stojnev/dwr-gwyfyn/Counterweight/STL/Counterweight - Counterweight Slider.stl

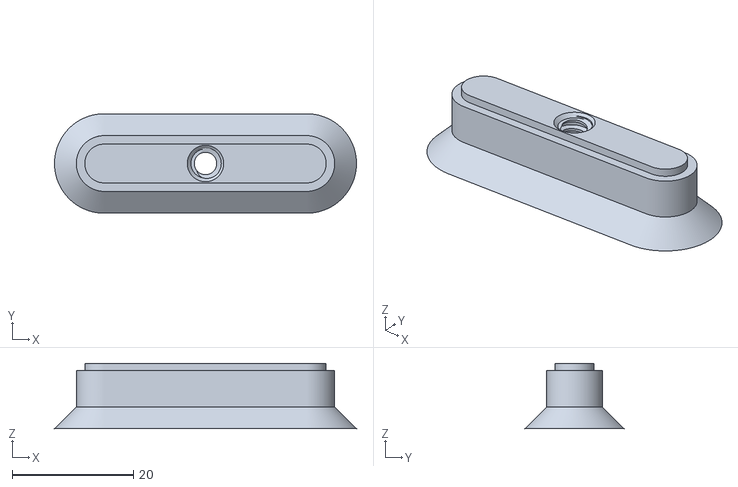
[picture p16: CAD file, 2026-01-21]
Counterweight/STL/Counterweight - Counterweight Slider.stl
49.8 x 16.4 x 10.8
