stojnev/dwr-gwyfyn/Pillar/STL/Tonearm Pillar - Pillar Body.stl

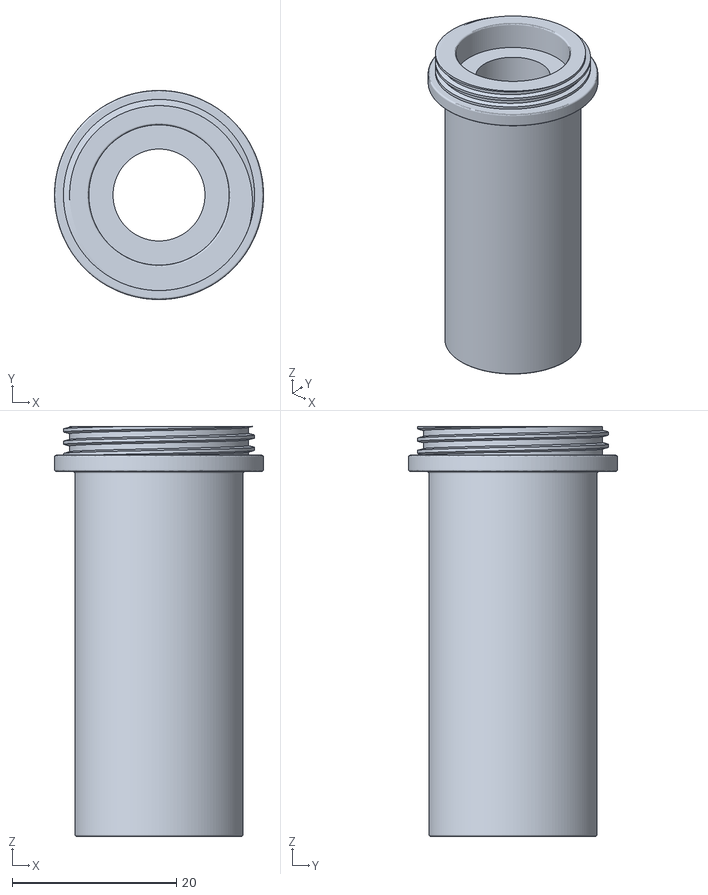
[picture p17: CAD file, 2026-01-14]
Pillar/STL/Tonearm Pillar - Pillar Body.stl
25.5 x 25.5 x 50.0
