stojnev/dwr-gwyfyn/Rest/STL/Tonearm Rest Modular - Tonearm Rest.stl

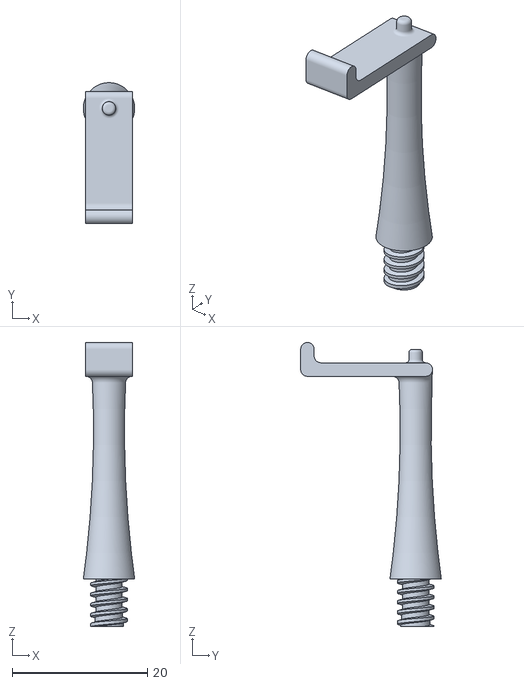
[picture p18: CAD file, 2026-01-17]
Rest/STL/Tonearm Rest Modular - Tonearm Rest.stl
7.60 x 20.8 x 42.0
