stojnev/dwr-gwyfyn/Tube/STL/Peripherals/Bearing Mount - Flexure Mount Cap.stl

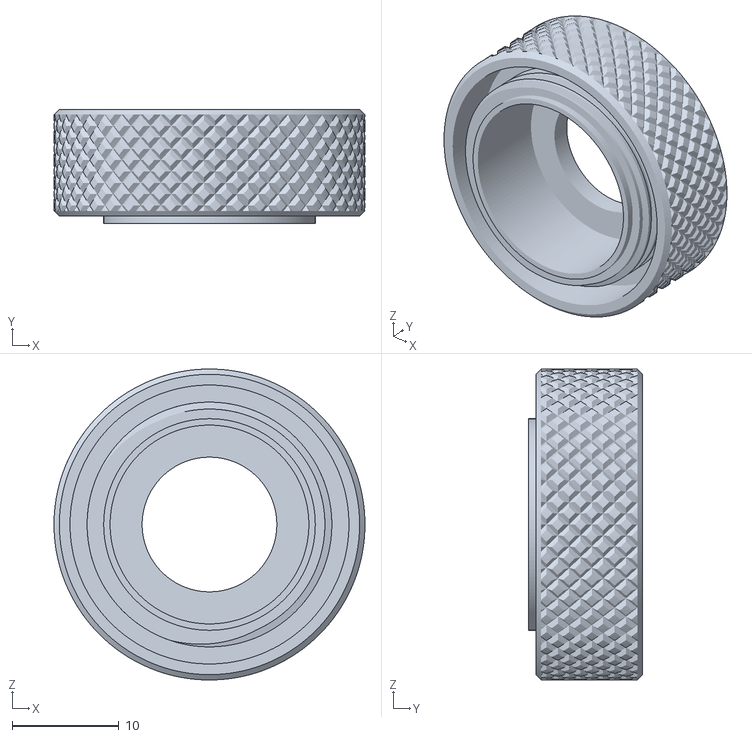
[picture p19: CAD file, 2026-02-07]
Tube/STL/Peripherals/Bearing Mount - Flexure Mount Cap.stl
29.1 x 10.7 x 29.1
