stojnev/dwr-gwyfyn/Base/STL/SME Mount - SME Clamp Collar.stl

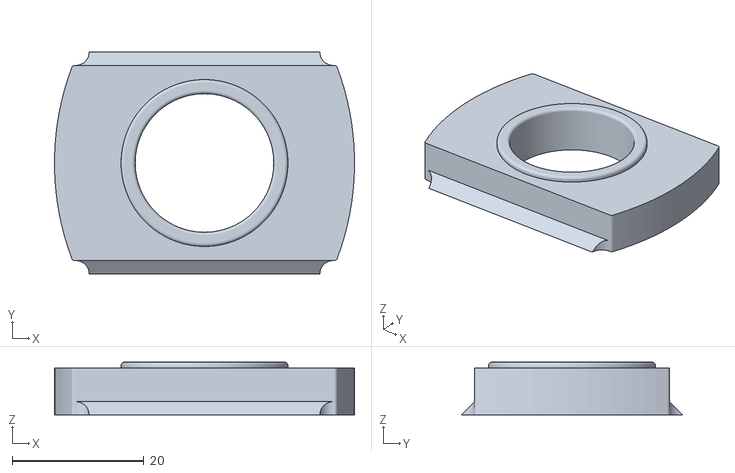
[picture p20: CAD file, 2026-01-13]
Base/STL/SME Mount - SME Clamp Collar.stl
45.5 x 33.6 x 8.00
