stojnev/dwr-gwyfyn/Counterweight/STL/Counterweight - Counterweight Base.stl

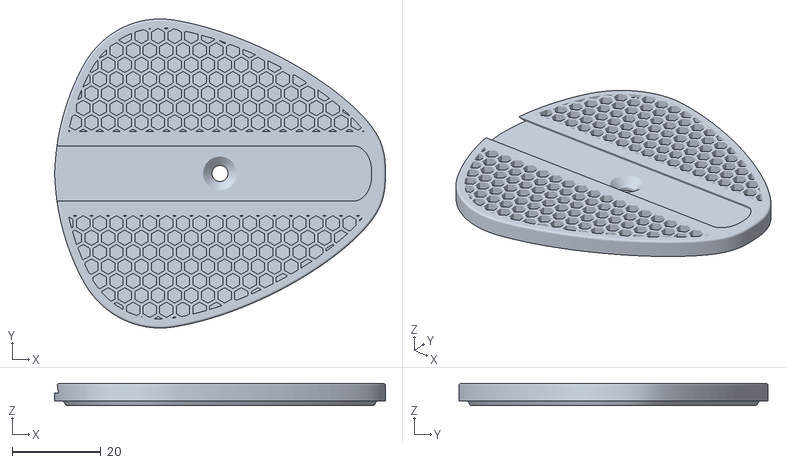
[picture p21: CAD file, 2026-01-21]
Counterweight/STL/Counterweight - Counterweight Base.stl
74.6 x 69.6 x 5.00
