stojnev/dwr-gwyfyn/Rest/STL/Tonearm Rest Modular - Connector Support.stl

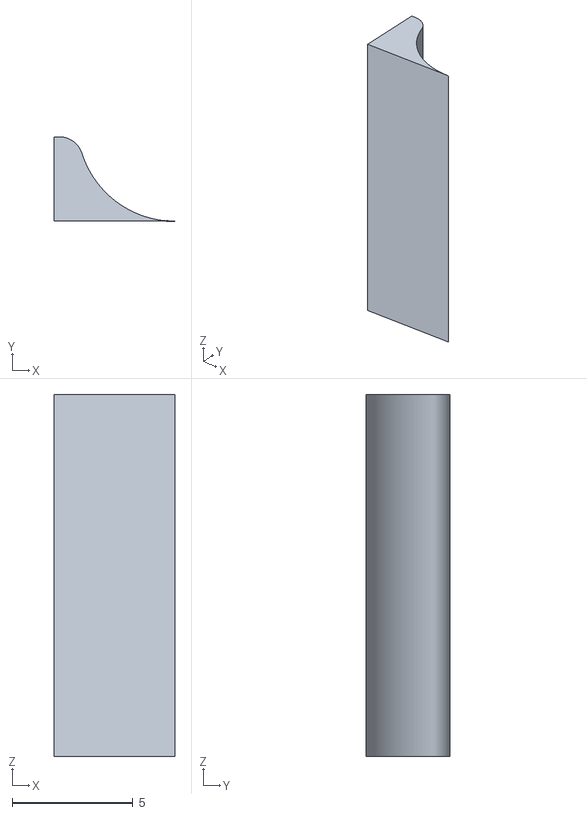
[picture p22: CAD file, 2026-01-17]
Rest/STL/Tonearm Rest Modular - Connector Support.stl
5.00 x 3.50 x 15.0
