stojnev/dwr-gwyfyn/Base/STL/SME Fixed Mount - SME Fixed Mount.stl

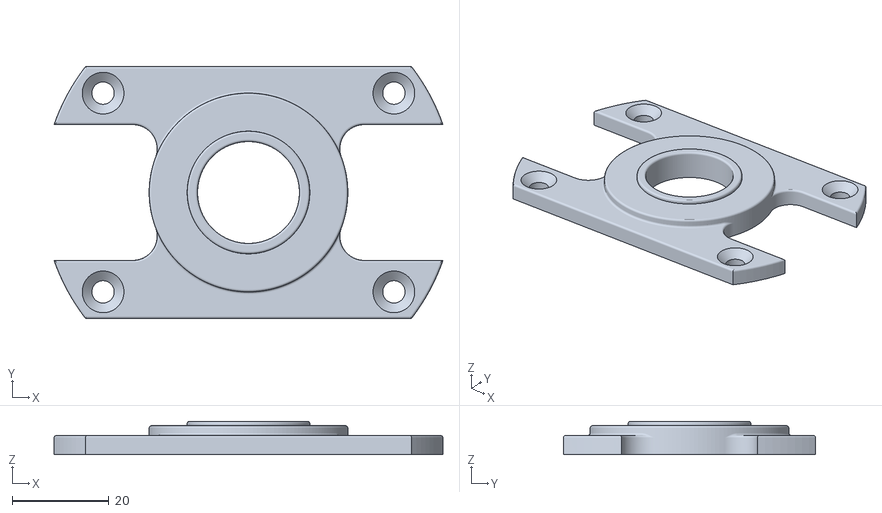
[picture p23: CAD file, 2026-01-13]
Base/STL/SME Fixed Mount - SME Fixed Mount.stl
80.3 x 52.0 x 6.90
