stojnev/dwr-gwyfyn/Rest/STL/Tonearm Rest Modular - Tonearm Plate.stl

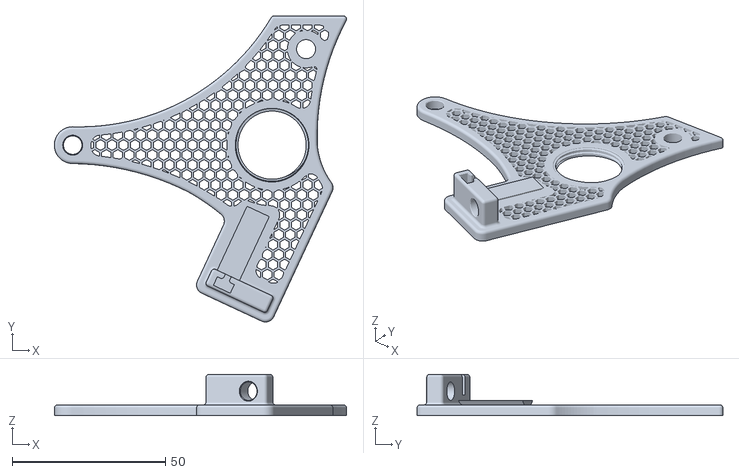
[picture p24: CAD file, 2026-01-17]
Rest/STL/Tonearm Rest Modular - Tonearm Plate.stl
95.3 x 99.7 x 13.5
