stojnev/dwr-gwyfyn/Base/STL/Helicoidal VTA - Adjustment Ring.stl

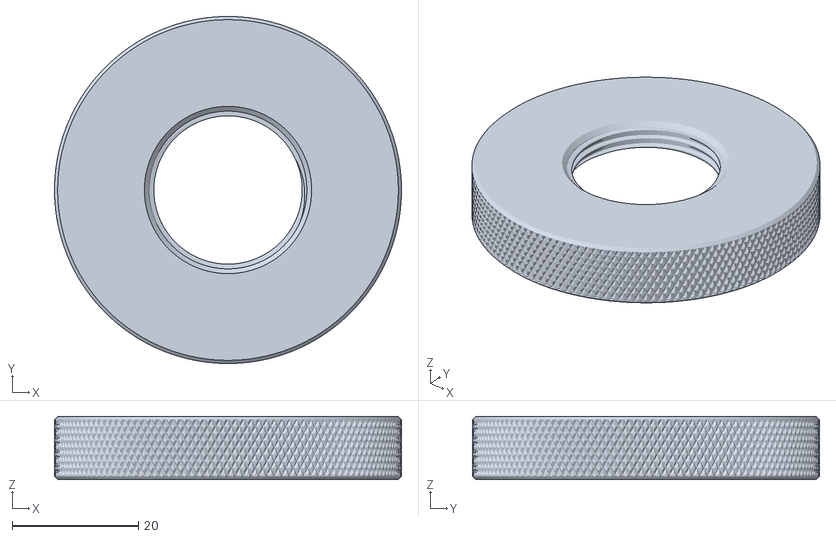
[picture p25: CAD file, 2026-01-13]
Base/STL/Helicoidal VTA - Adjustment Ring.stl
55.0 x 55.0 x 10.0
