stojnev/dwr-gwyfyn/Base/STL/Helicoidal VTA - VTA Base.stl

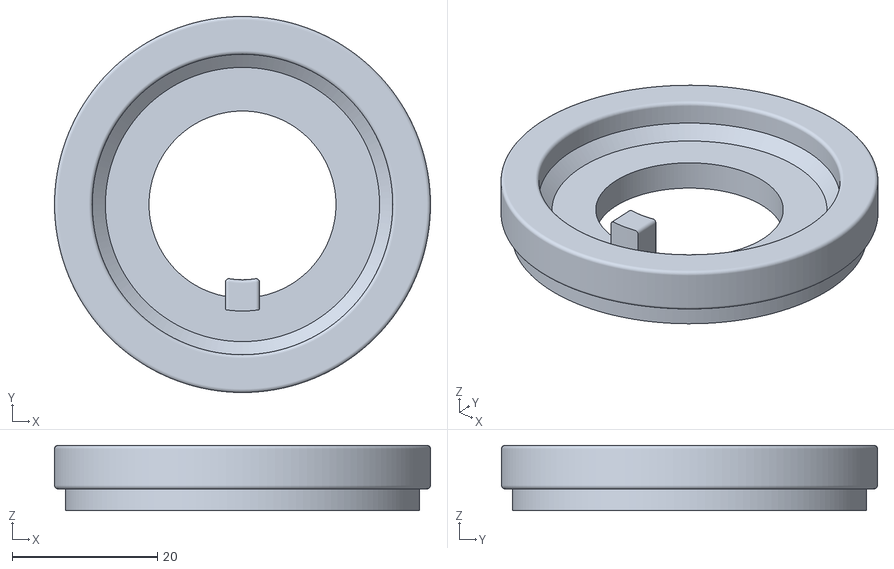
[picture p26: CAD file, 2026-01-13]
Base/STL/Helicoidal VTA - VTA Base.stl
51.7 x 51.7 x 9.00
