stojnev/dwr-gwyfyn/Rest/STL/Tonearm Rest Modular - Wiring Cover RCA.stl

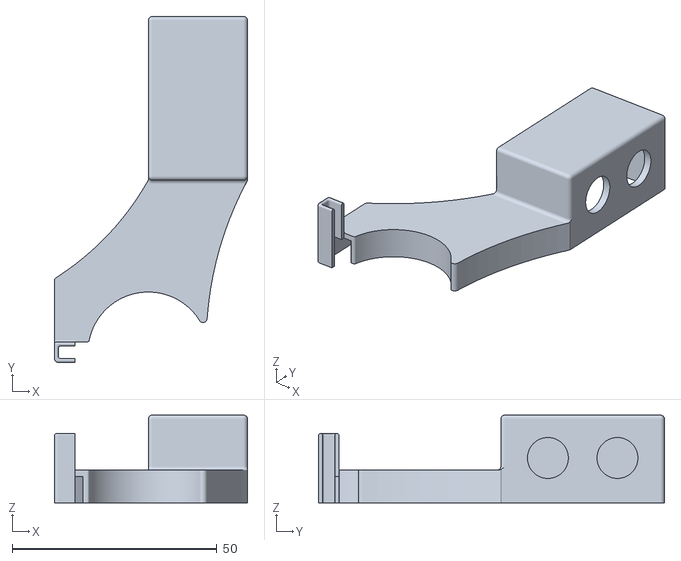
[picture p27: CAD file, 2026-01-17]
Rest/STL/Tonearm Rest Modular - Wiring Cover RCA.stl
47.3 x 84.6 x 21.5
