stojnev/dwr-gwyfyn/Base/STL/SME Mount - SME Base.stl

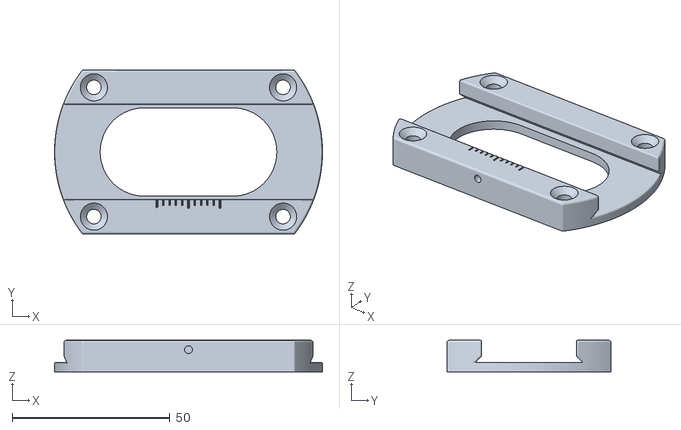
[picture p28: CAD file, 2026-01-13]
Base/STL/SME Mount - SME Base.stl
85.0 x 52.0 x 10.0
