stojnev/dwr-gwyfyn/Rest/STL/Tonearm Rest Modular - Wiring Cover DIN.stl

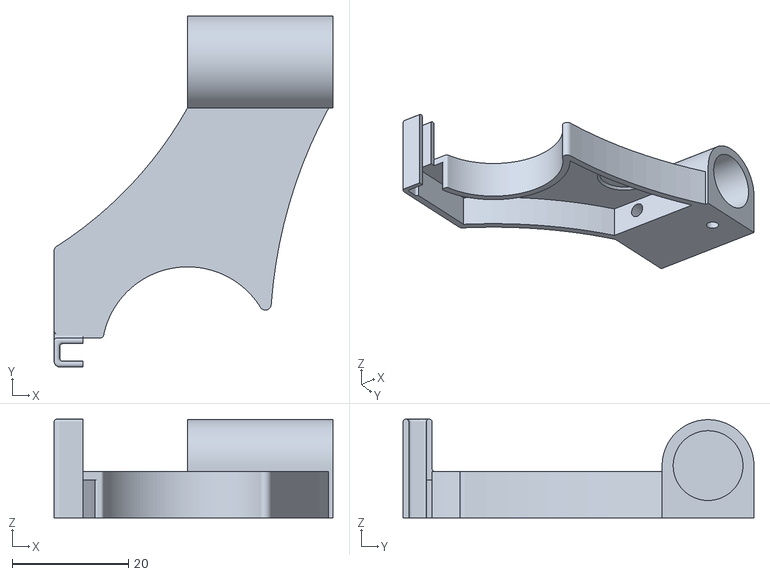
[picture p29: CAD file, 2026-01-17]
Rest/STL/Tonearm Rest Modular - Wiring Cover DIN.stl
48.0 x 60.4 x 17.0
