stojnev/dwr-gwyfyn/Base/STL/Helicoidal VTA - Tonearm Collar.stl

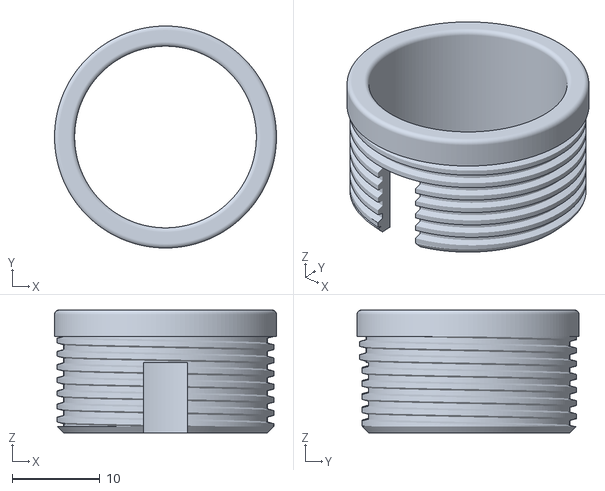
[picture p30: CAD file, 2026-01-13]
Base/STL/Helicoidal VTA - Tonearm Collar.stl
25.3 x 25.3 x 14.0
