stojnev/dwr-gwyfyn/Alignment/Spindle Distance Jig/Assemblies/Spindle Distance Jig Universal.png

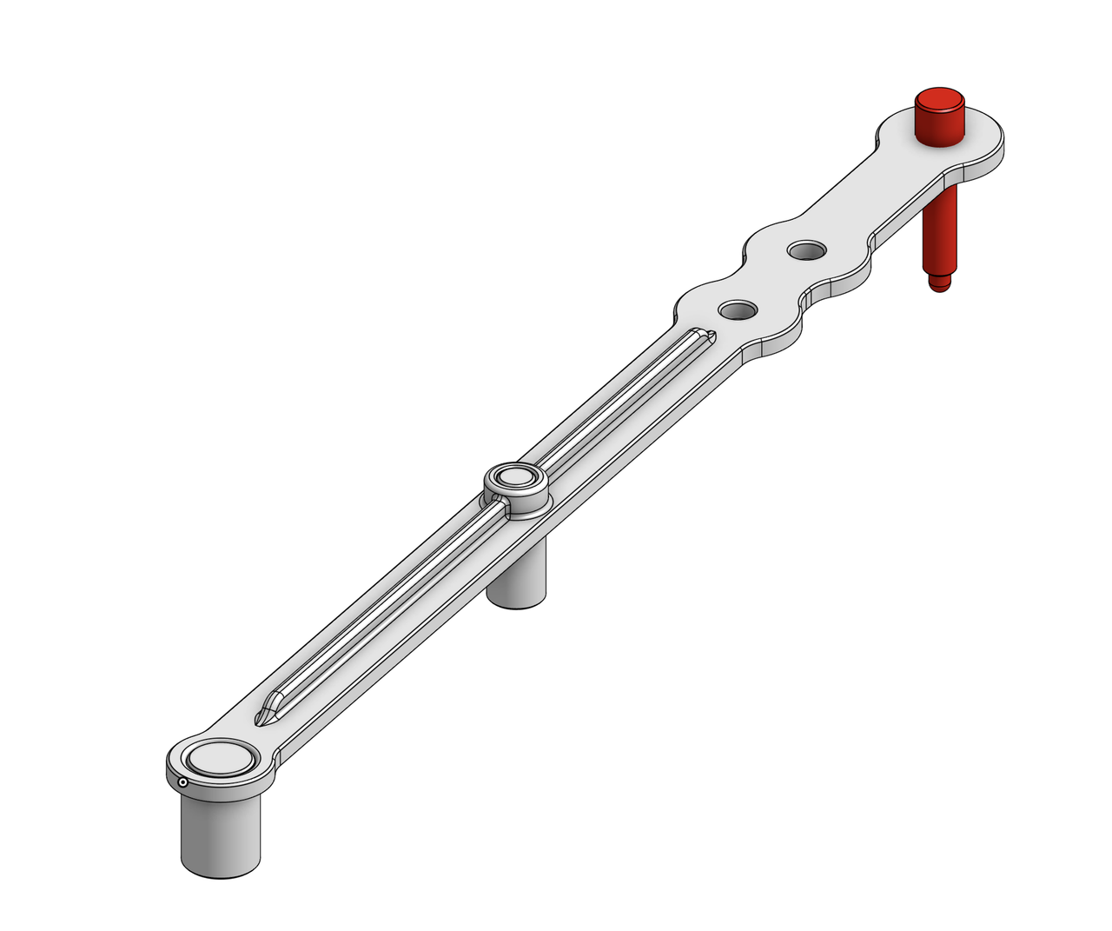
Alignment/Spindle Distance Jig/Assemblies/Spindle Distance Jig Universal.png
