stojnev/dwr-gwyfyn/Alignment/Spindle Distance Jig/Assemblies/Spindle Distance Jig.png

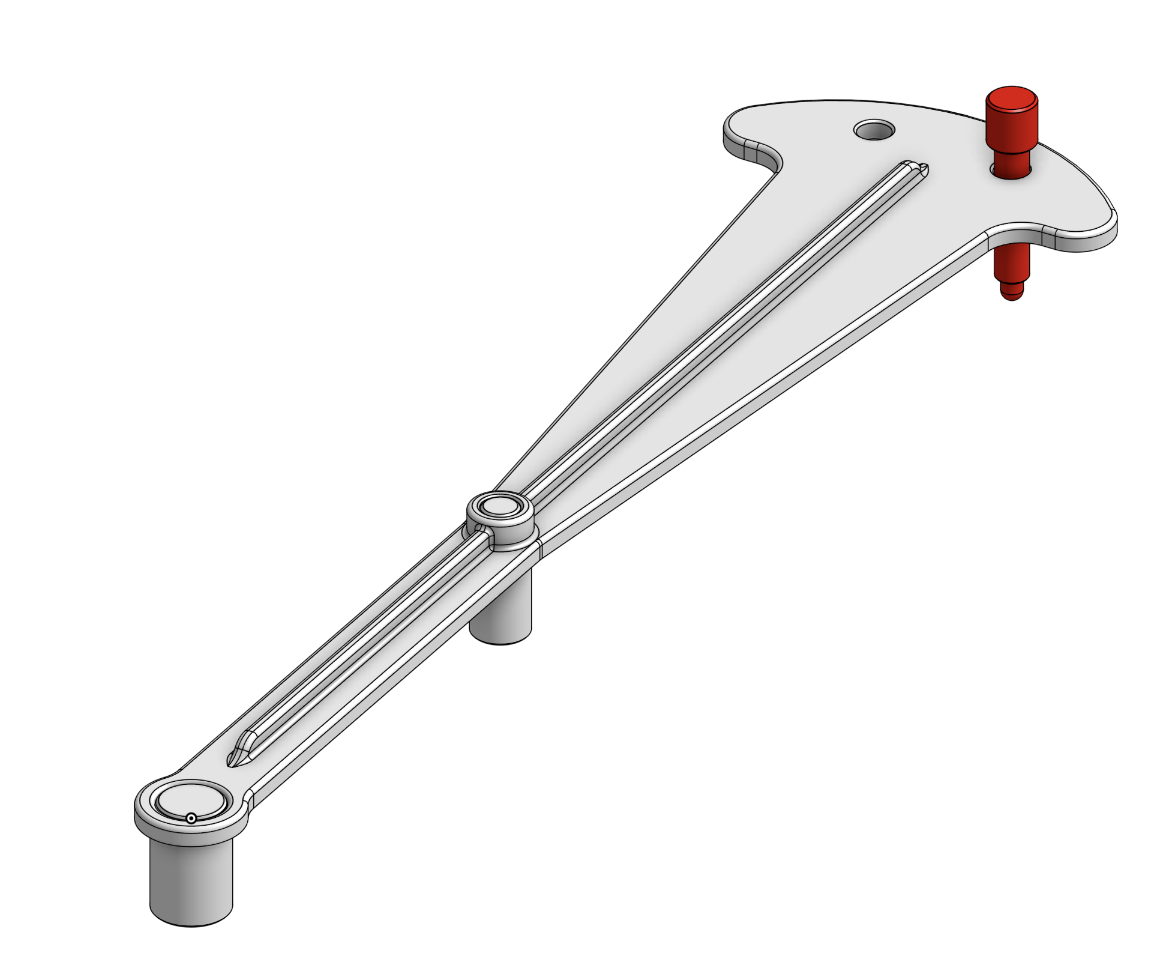
Alignment/Spindle Distance Jig/Assemblies/Spindle Distance Jig.png
