stojnev/dwr-gwyfyn/Base/Assemblies/SME Fixed VTA Clamp Mount [FULL].png

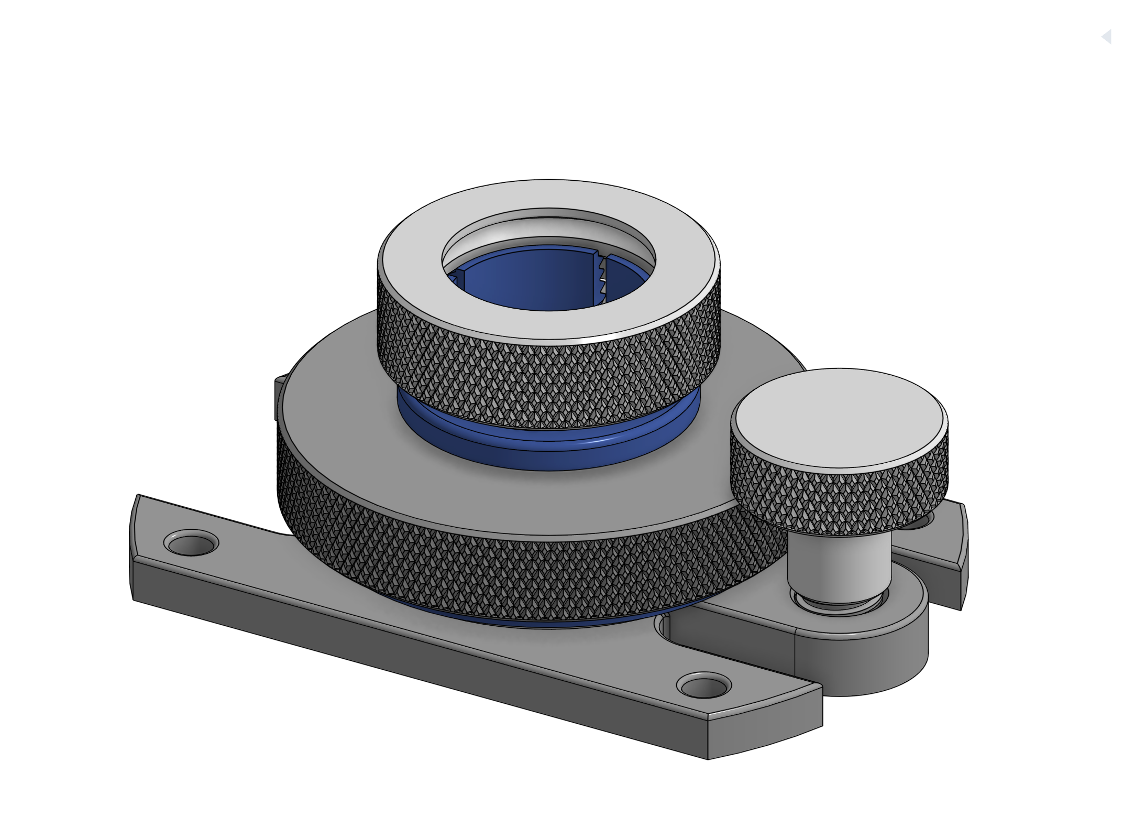
Base/Assemblies/SME Fixed VTA Clamp Mount [FULL].png
