stojnev/dwr-gwyfyn/Base/Assemblies/SME Sliding Clamp Mount [FULL].png

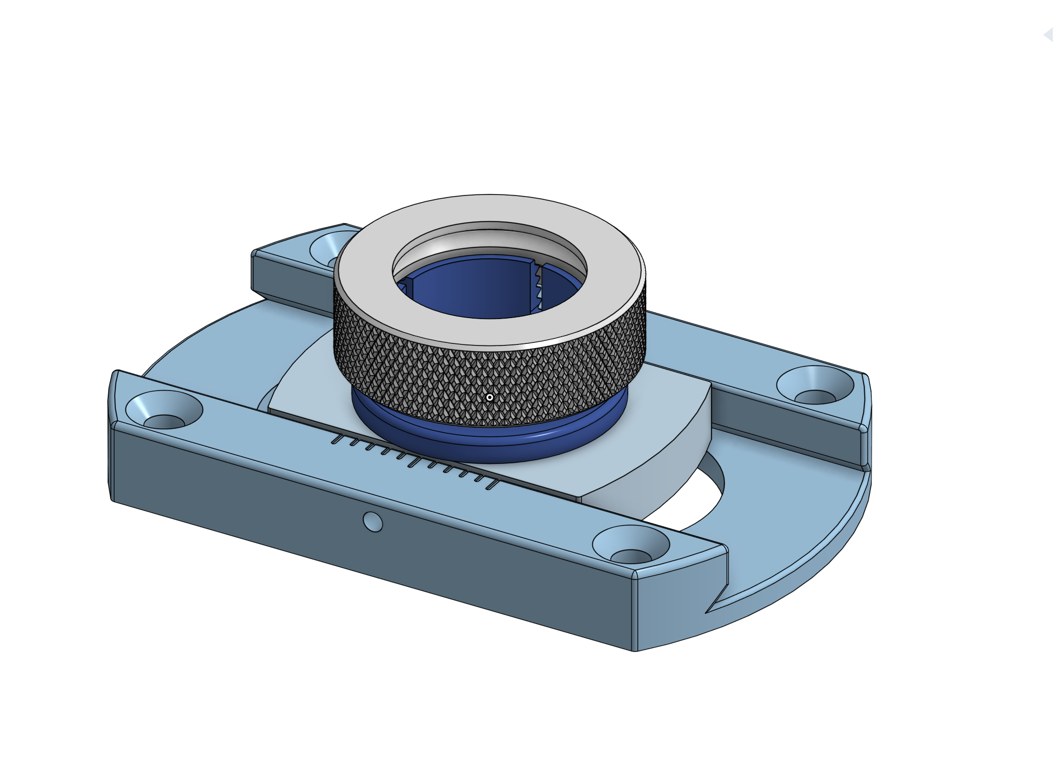
Base/Assemblies/SME Sliding Clamp Mount [FULL].png
