stojnev/dwr-gwyfyn/Counterweight/Assemblies/Counterweight [FULL].png

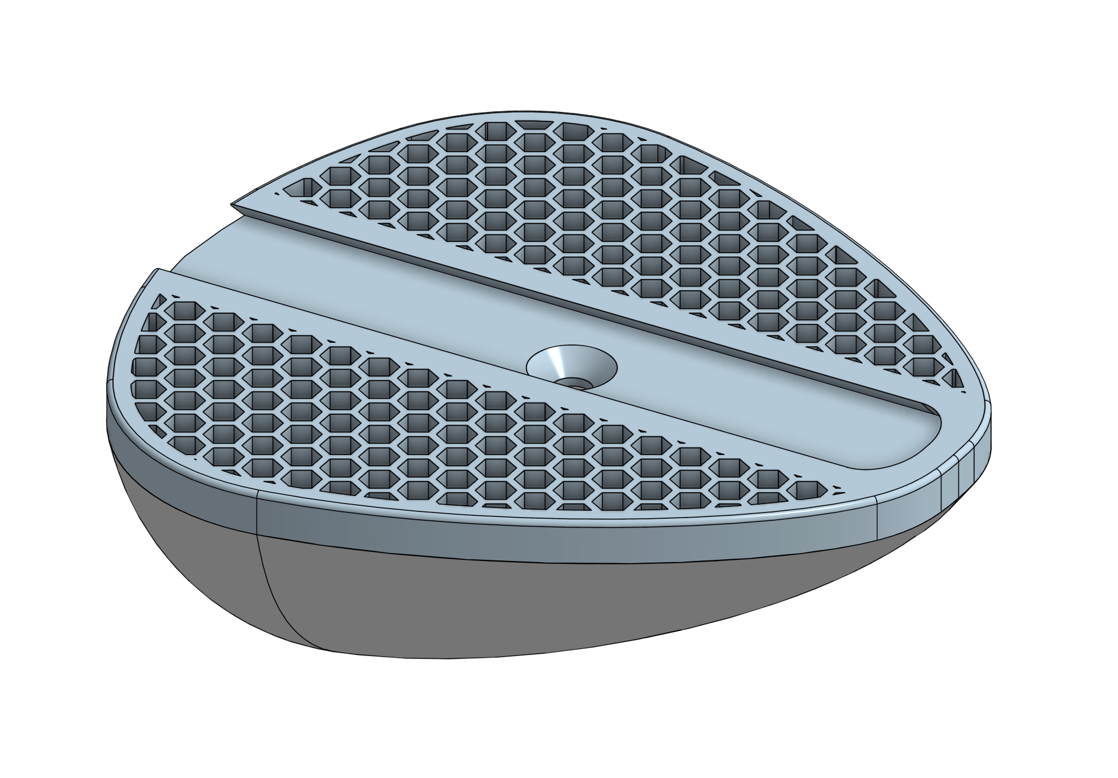
Counterweight/Assemblies/Counterweight [FULL].png
