stojnev/dwr-gwyfyn/Pillar/Assemblies/Tonearm Pillar [FULL].png

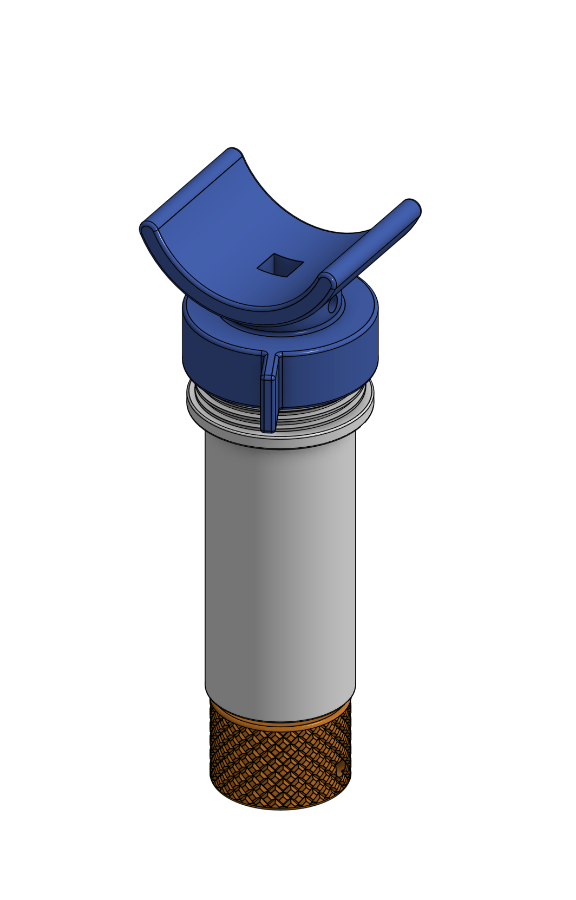
Pillar/Assemblies/Tonearm Pillar [FULL].png
