stojnev/dwr-gwyfyn/Rest/Assemblies/Tonearm Rest Modular DIN [FULL].png

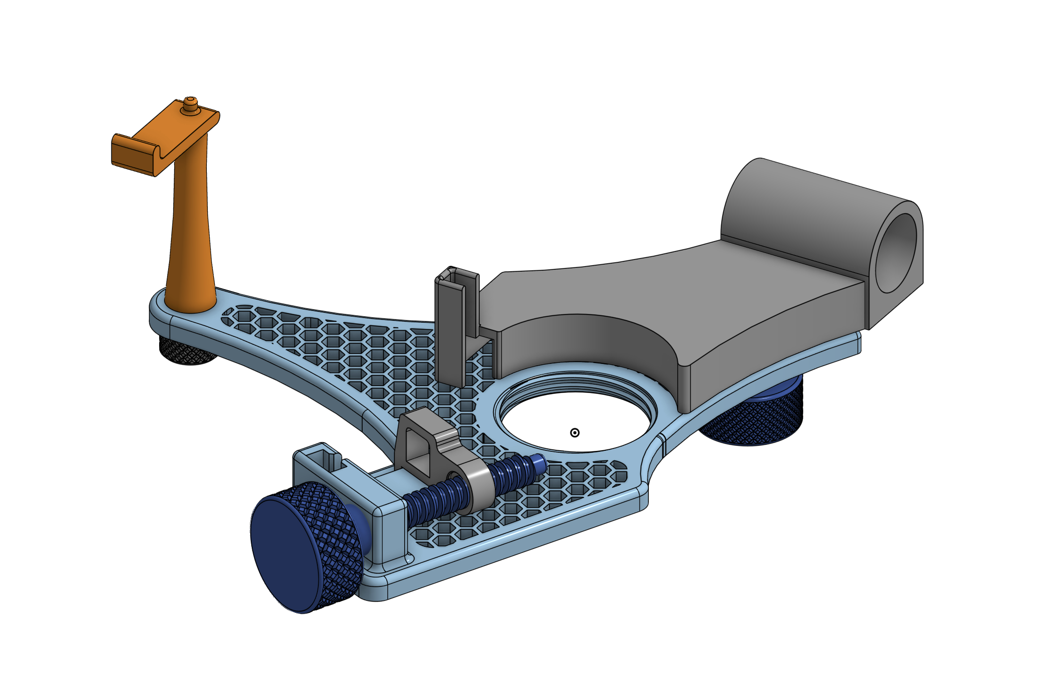
Rest/Assemblies/Tonearm Rest Modular DIN [FULL].png
